supercrab/AlexaLamp/images/wifi-manager-home.jpg

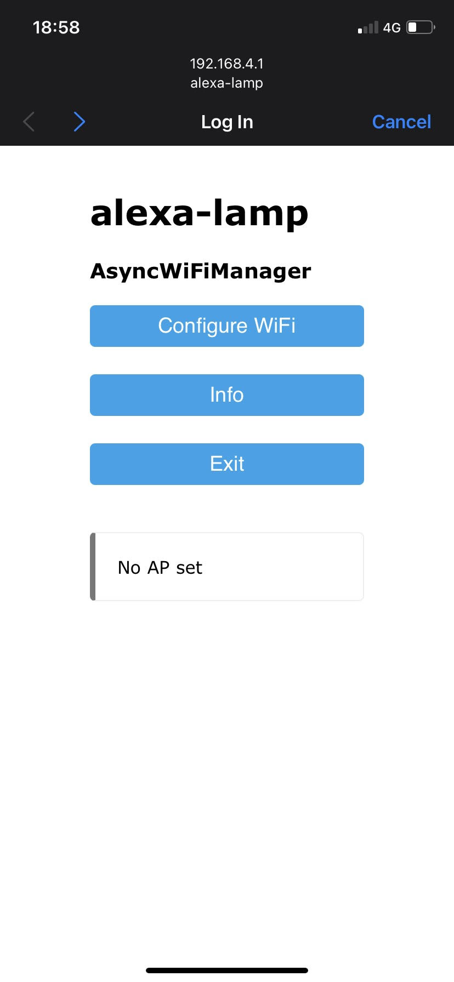
images/wifi-manager-home.jpg
