supercrab/AlexaLamp/design/layout.sch

## EAGLE design design/layout.sch (2020-03-13)

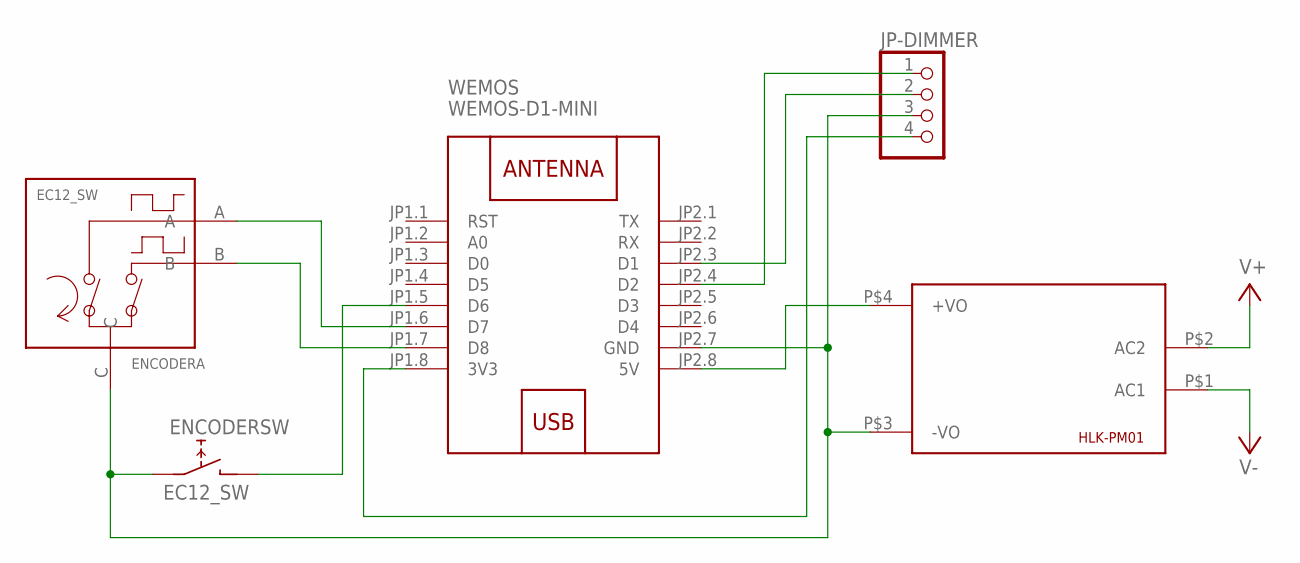
[picture p14: schematic layout.sch]

Parts:
ENCODER: EC12_SW; EC12S
HLK-PM01: HLK-PM013W; HLK-PM01
JP-DIMMER: PINHD-1X4; 1X04
WEMOS: WEMOS-D1-MINI

Connections:
unnamed: ENCODER.C, ENCODER.D, HLK-PM01.P$3 (-VO), JP-DIMMER.3, WEMOS.JP2.7 (GND)
unnamed: HLK-PM01.P$4 (+VO), WEMOS.JP2.8 (5V)
unnamed: ENCODER.A, WEMOS.JP1.6 (D7)
unnamed: ENCODER.B, WEMOS.JP1.7 (D8)
unnamed: ENCODER.E, WEMOS.JP1.5 (D6)
unnamed: JP-DIMMER.4, WEMOS.JP1.8 (3V3)
unnamed: JP-DIMMER.2, WEMOS.JP2.3 (D1)
unnamed: JP-DIMMER.1, WEMOS.JP2.4 (D2)
V+: HLK-PM01.P$2 (AC2)
V-: HLK-PM01.P$1 (AC1)
