supercrab/AlexaLamp/fauxmoESP.h

/*

FAUXMO ESP

Copyright (C) 2016-2020 by Xose Pérez <xose dot perez at gmail dot com>

The MIT License (MIT)

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
*/

#pragma once

#define FAUXMO_UDP_MULTICAST_IP     IPAddress(239,255,255,250)
#define FAUXMO_UDP_MULTICAST_PORT   1900
#define FAUXMO_TCP_MAX_CLIENTS      10
#define FAUXMO_TCP_PORT             1901
#define FAUXMO_RX_TIMEOUT           3
#define FAUXMO_DEVICE_UNIQUE_ID_LENGTH  12

//#define DEBUG_FAUXMO                Serial
#ifdef DEBUG_FAUXMO
    #if defined(ARDUINO_ARCH_ESP32)
        #define DEBUG_MSG_FAUXMO(fmt, ...) { DEBUG_FAUXMO.printf_P((PGM_P) PSTR(fmt), ## __VA_ARGS__); }
    #else
        #define DEBUG_MSG_FAUXMO(fmt, ...) { DEBUG_FAUXMO.printf(fmt, ## __VA_ARGS__); }
    #endif
#else
    #define DEBUG_MSG_FAUXMO(...)
#endif

#ifndef DEBUG_FAUXMO_VERBOSE_TCP
#define DEBUG_FAUXMO_VERBOSE_TCP    false
#endif

#ifndef DEBUG_FAUXMO_VERBOSE_UDP
#define DEBUG_FAUXMO_VERBOSE_UDP    false
#endif

#include <Arduino.h>

#if defined(ESP8266)
    #include <ESP8266WiFi.h>
    #include <ESPAsyncTCP.h>
#elif defined(ESP32)
    #include <WiFi.h>
    #include <AsyncTCP.h>
#else
	#error Platform not supported
#endif

#include <WiFiUdp.h>
#include <functional>
#include <vector>
#include <MD5Builder.h>
#include "fauxmoTemplates.h"

typedef std::function<void(unsigned char, const char *, bool, unsigned char)> TSetStateCallback;

typedef struct {
    char * name;
    bool state;
    unsigned char value;
    char uniqueid[28];
} fauxmoesp_device_t;

class fauxmoESP {

    public:

        ~fauxmoESP();

        unsigned char addDevice(const char * device_name);
        bool renameDevice(unsigned char id, const char * device_name);
        bool renameDevice(const char * old_device_name, const char * new_device_name);
        bool removeDevice(unsigned char id);
        bool removeDevice(const char * device_name);
        char * getDeviceName(unsigned char id, char * buffer, size_t len);
        int getDeviceId(const char * device_name);
        void setDeviceUniqueId(unsigned char id, const char *uniqueid);
        void onSetState(TSetStateCallback fn) { _setCallback = fn; }
        bool setState(unsigned char id, bool state, unsigned char value);
        bool setState(const char * device_name, bool state, unsigned char value);
        bool process(AsyncClient *client, bool isGet, String url, String body);
        void enable(bool enable);
        void createServer(bool internal) { _internal = internal; }
        void setPort(unsigned long tcp_port) { _tcp_port = tcp_port; }
        void setRedirect(unsigned long redirect_port) { _redirect_port = redirect_port; }
        void handle();

    private:

        AsyncServer * _server;
        bool _enabled = false;
        bool _internal = true;
        unsigned int _tcp_port = FAUXMO_TCP_PORT;
        unsigned int _redirect_port = 0;
        std::vector<fauxmoesp_device_t> _devices;
		#ifdef ESP8266
        WiFiEventHandler _handler;
		#endif
        WiFiUDP _udp;
        AsyncClient * _tcpClients[FAUXMO_TCP_MAX_CLIENTS];
        TSetStateCallback _setCallback = NULL;

        String _deviceJson(unsigned char id, bool all); 	// all = true means we are listing all devices so use full description template

        void _handleUDP();
        void _onUDPData(const IPAddress remoteIP, unsigned int remotePort, void *data, size_t len);
        void _sendUDPResponse();

        void _onTCPClient(AsyncClient *client);
        bool _onTCPData(AsyncClient *client, void *data, size_t len);
        bool _onTCPRequest(AsyncClient *client, bool isGet, String url, String body);
        bool _onTCPDescription(AsyncClient *client, String url, String body);
        bool _onTCPList(AsyncClient *client, String url, String body);
        bool _onTCPControl(AsyncClient *client, String url, String body);
        void _sendTCPResponse(AsyncClient *client, const char * code, char * body, const char * mime);

        String _byte2hex(uint8_t zahl);
        String _makeMD5(String text);
};
